holla2040/lucky7/src/RC65X.h

#ifndef  _IRRC65X
#define  _IRRC65X 1

#define RC65X_KEYTVINPUT    0x38C34200
#define RC65X_KEYPWR        0xA80E7E5E
#define RC65X_KEYON         0x38C34200

#define RC65X_KEYPREVIOUS   0xE6D07133
#define RC65X_KEYREPLAY     0x21FEFDF9
#define RC65X_KEYSTOP       0xFBAD8623
#define RC65X_KEYADVANCE    0x9D71047C
#define RC65X_KEYNEXT       0x9B72C267
#define RC65X_KEYPLAY       0x9A6F0576
#define RC65X_KEYPAUSE      0xD049E0A6
#define RC65X_KEYRECORD     0x81A840E6

#define RC65X_KEYGUIDE      0x427EBE9F
#define RC65X_KEYACTIVE     0x9D65B0BC
#define RC65X_KEYLIST       0xAB4D94A9
#define RC65X_KEYEXIT       0x34498102

#define RC65X_KEYUP         0xF24119FE
#define RC65X_KEYRIGHT      0x0BC9DF06
#define RC65X_KEYDOWN       0xB489062B
#define RC65X_KEYLEFT       0xC53794B4
#define RC65X_KEYSELECT     0x75A956A7

#define RC65X_KEYBACK       0xBB9BDEE7
#define RC65X_KEYMENU       0x76CF1379
#define RC65X_KEYINFO       0x0F640360

#define RC65X_KEYRED        0xC332FABB
#define RC65X_KEYGREEN      0x8C0B38A3
#define RC65X_KEYYELLOW     0x2591C110
#define RC65X_KEYBLUE       0x506AE98B

#define RC65X_KEYVOLUMEUP   0x38C34200
#define RC65X_KEYVOLUMEDOWN 0x38C34200

#define RC65X_KEYCHANUP     0x165412B7
#define RC65X_KEYCHANDOWN   0x5815B090

#define RC65X_KEYMUTE       0x38C34200
#define RC65X_KEYPREV       0x5BFBFDE9

#define RC65X_KEY1          0xC9767F76
#define RC65X_KEY2          0xC8155AB1
#define RC65X_KEY3          0xB6996DAE
#define RC65X_KEY4          0x969AE844
#define RC65X_KEY5          0x4AAFAC67
#define RC65X_KEY6          0x9C2A936C
#define RC65X_KEY7          0x833ED333
#define RC65X_KEY8          0x55F2B93
#define RC65X_KEY9          0xDE78B0D0
#define RC65X_KEYDASH       0xBDE97C12
#define RC65X_KEY0          0xF32F72D7
#define RC65X_KEYENTER      0x03F23F43

#endif
