holla2040/lucky7/src/RMYD065.h

#ifndef  _IRRMYD065
#define  _IRRMYD065 1

/* got this from lirc RM-ED035 and RM-YD010 */

#define RM_YD065_KEYINPUT                    0xA50
#define RM_YD065_KEYSTANDBY                  0xA90
#define RM_YD065_KEYEXIT                     0xC70
/* ??? #define RM_YD065_KEY-                     0x5D0 */
#define RM_YD065_KEYHOME                     0x070
#define RM_YD065_KEYOK                       0xA70
#define RM_YD065_KEYUP                       0x2F0
#define RM_YD065_KEYRIGHT                    0xCD0
#define RM_YD065_KEYDOWN                     0xAF0
#define RM_YD065_KEYLEFT                     0x2D0
#define RM_YD065_KEY1                        0x010
#define RM_YD065_KEY2                        0x810
#define RM_YD065_KEY3                        0x410
#define RM_YD065_KEY4                        0xC10
#define RM_YD065_KEY5                        0x210
#define RM_YD065_KEY6                        0xA10
#define RM_YD065_KEY7                        0x610
#define RM_YD065_KEY8                        0xE10
#define RM_YD065_KEY9                        0x110
#define RM_YD065_KEYTELETEXT                 0xFD0
#define RM_YD065_KEY0                        0x910
#define RM_YD065_KEYMUTE                     0x290
#define RM_YD065_KEYVOLUMEUP                 0x490
#define RM_YD065_KEYVOLUMEDOWN               0xC90
#define RM_YD065_KEYPROGUP                   0x090
#define RM_YD065_KEYPROGDOWN                 0x890
#define RM_YD065_KEYAUDIO                    0xE90
#define RM_YD065_KEYBACK_STANDBY             0xA90

#define RM_YD065_KEYJUMP                     0xDD0

#define RM_YD065_KEYSYNCMENU                 0x0D58
#define RM_YD065_KEYPREVIOUS                 0x1EE9
#define RM_YD065_KEYSTOP                     0x0CE9
#define RM_YD065_KEYPAUSE                    0x4CE9
#define RM_YD065_KEYNEXT                     0x5EE9
/* ???  #define RM_YD065_KEYI-MANUAL                 0x6F58 */
#define RM_YD065_KEYSCENE                    0x0F58
#define RM_YD065_KEYASPECT_RATIO             0x5E25
#define RM_YD065_KEYDIGITAL_ANALOG           0x58EE
#define RM_YD065_KEYTHEATRE                  0x03EE
#define RM_YD065_KEYFBACKWARD                0x6CE9
#define RM_YD065_KEYPLAY                     0x2CE9
#define RM_YD065_KEYFFORWARD                 0x1CE9
#define RM_YD065_KEYINTERNET_VIDEO           0x4F58
#define RM_YD065_KEYGUIDE                    0x6D25
#define RM_YD065_KEYFAVORITES                0x37EE
#define RM_YD065_KEYOPTIONS                  0x36E9
#define RM_YD065_KEYRETURN                   0x62E9
#define RM_YD065_KEYRED                      0x52E9
#define RM_YD065_KEYGREEN                    0x32E9
#define RM_YD065_KEYYELLOW                   0x72E9
#define RM_YD065_KEYBLUE                     0x12E9
#define RM_YD065_KEYSUBTITLES                0x0AE9
#define RM_YD065_KEYDECIMALPOINT             0x5CE9



#endif
